Frauschi/Funktionsgenerator/Bilder/Gerät/Frontansicht.png

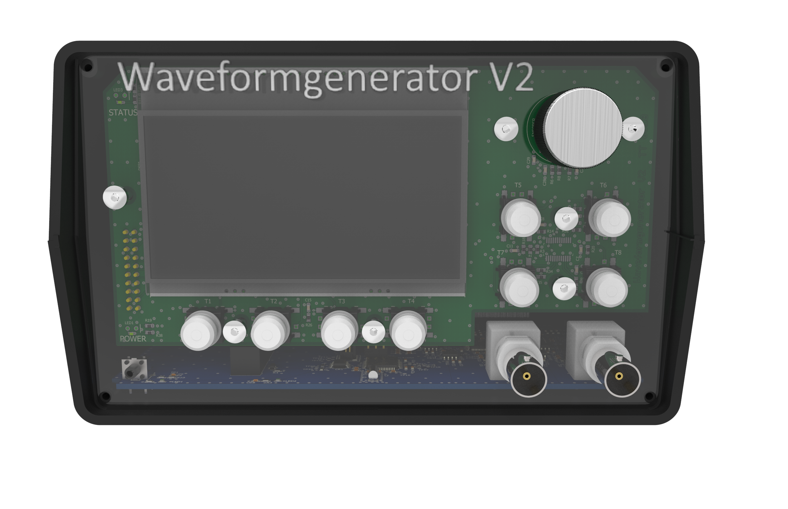
Bilder/Gerät/Frontansicht.png
