Frauschi/Funktionsgenerator/Bilder/Gerät/Frontpanel.png

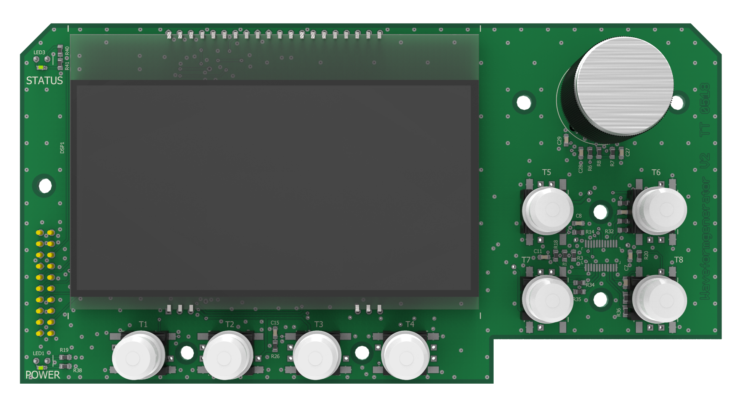
Bilder/Gerät/Frontpanel.png
