Frauschi/Funktionsgenerator/Bilder/Gerät/Funktionsgenerator_fertig2.jpg

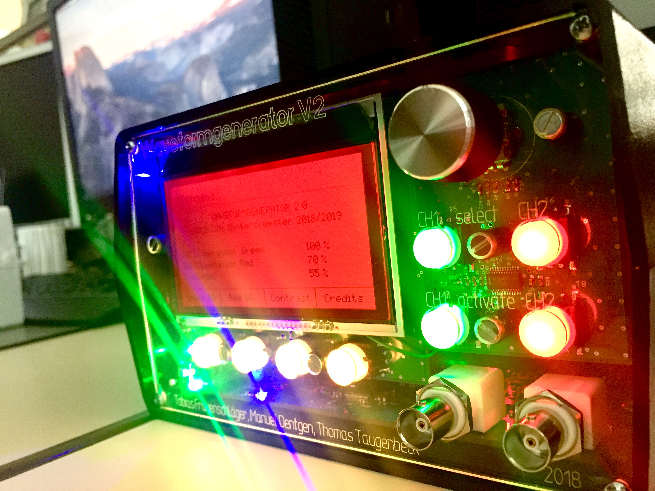
Bilder/Gerät/Funktionsgenerator_fertig2.jpg
