Frauschi/Funktionsgenerator/Bilder/Gerät/Innenansicht_oben.png

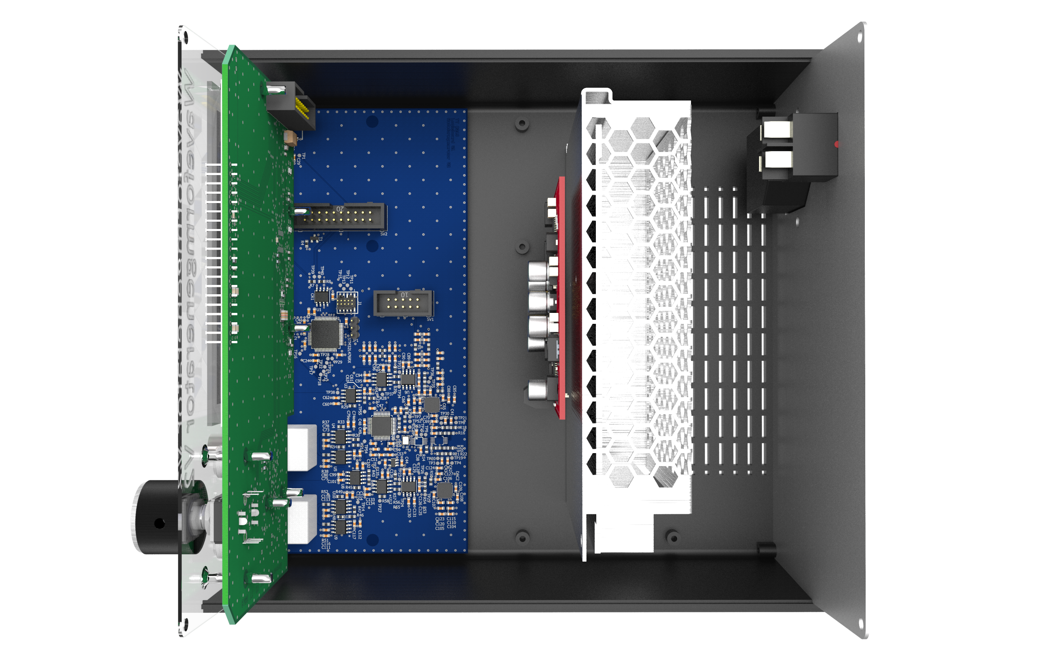
Bilder/Gerät/Innenansicht_oben.png
