Frauschi/Funktionsgenerator/Bilder/Gerät/Rückansicht.jpg

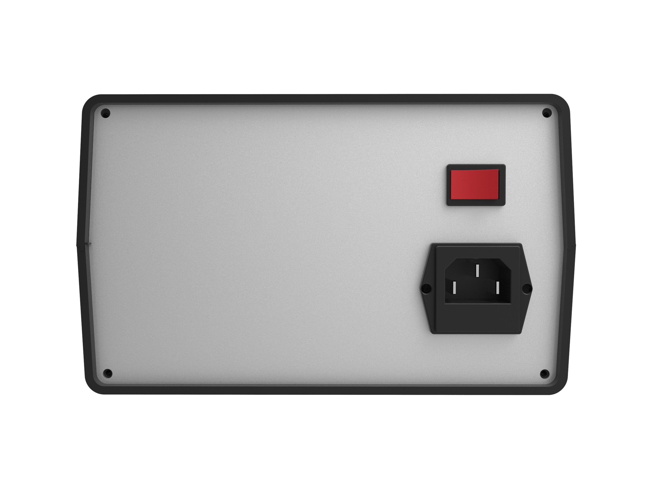
Bilder/Gerät/Rückansicht.jpg
