Frauschi/Funktionsgenerator/Bilder/Signale/Rect_1Hz.png

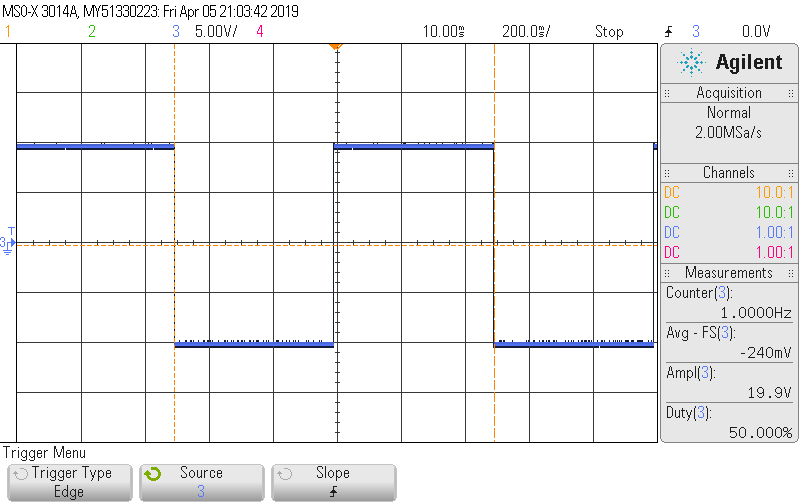
Bilder/Signale/Rect_1Hz.png
