Frauschi/Funktionsgenerator/Bilder/Signale/Rect_1MHz.png

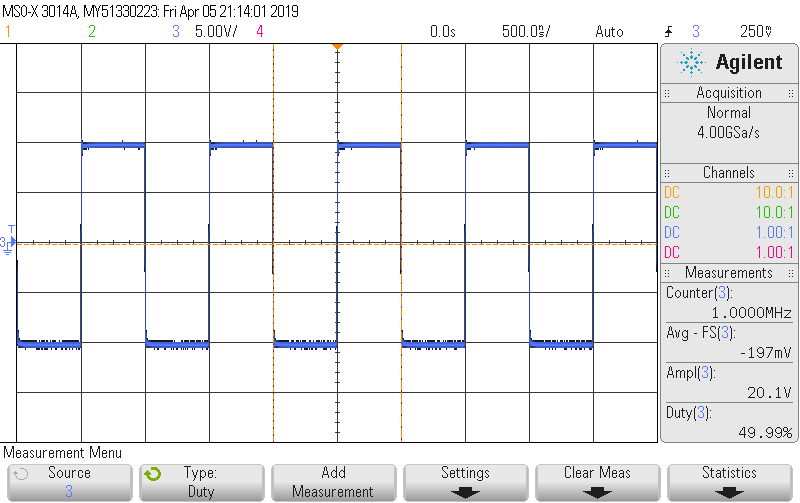
Bilder/Signale/Rect_1MHz.png
