Frauschi/Funktionsgenerator/Bilder/Signale/Rect_1MHz_10%.png

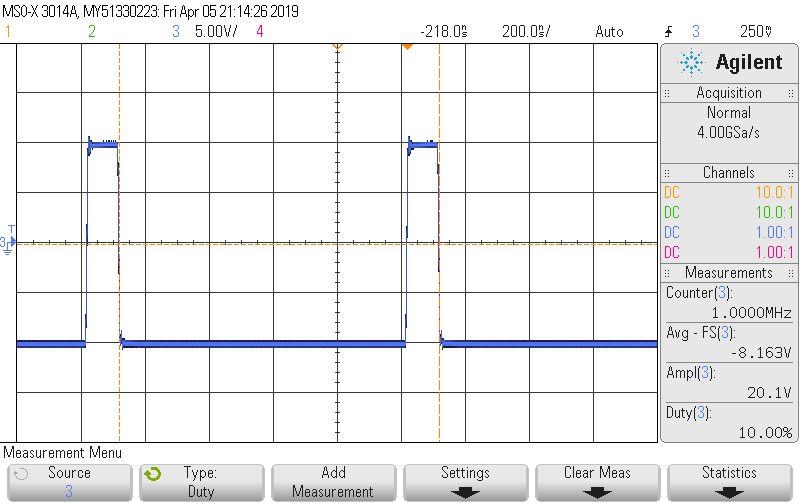
Bilder/Signale/Rect_1MHz_10%.png
