Frauschi/Funktionsgenerator/Bilder/Signale/Rect_1MHz_90%.png

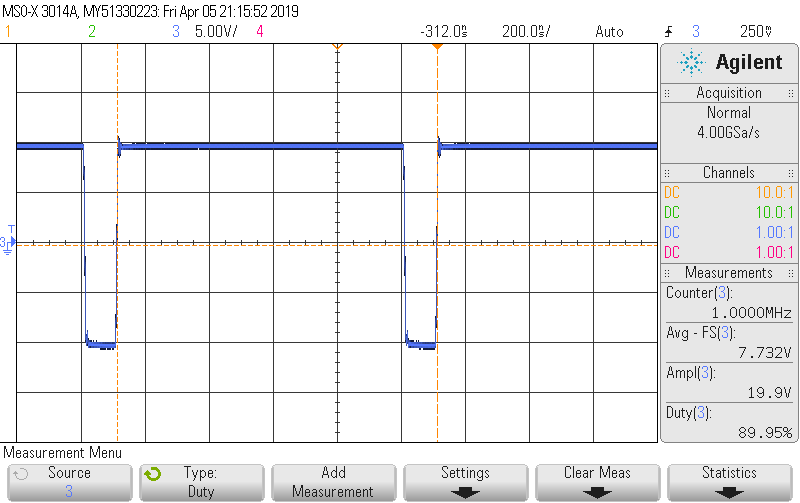
Bilder/Signale/Rect_1MHz_90%.png
