Frauschi/Funktionsgenerator/Bilder/Signale/Rect_10MHz.png

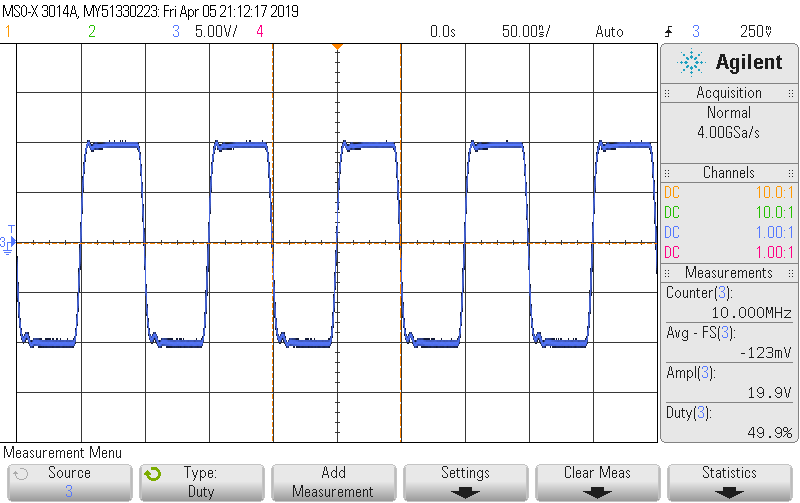
Bilder/Signale/Rect_10MHz.png
