Frauschi/Funktionsgenerator/Bilder/Signale/Saw_neg_1Hz.png

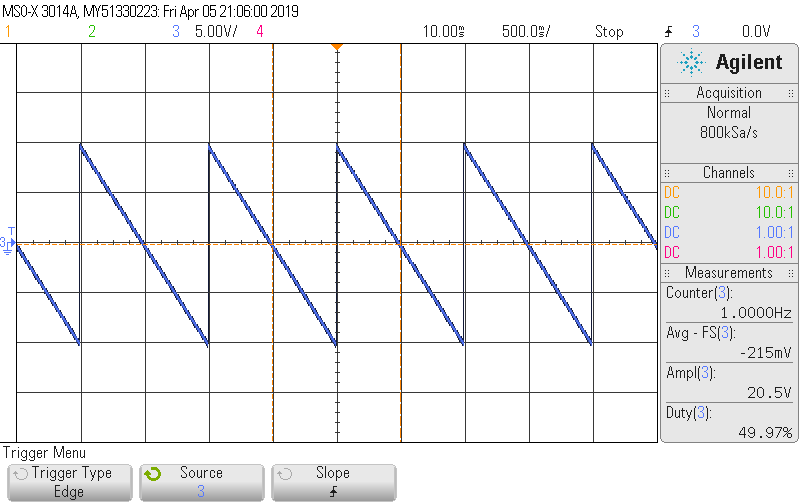
Bilder/Signale/Saw_neg_1Hz.png
