Frauschi/Funktionsgenerator/Bilder/Signale/Sine_1MHz_2Vpp_1V_Offset.png

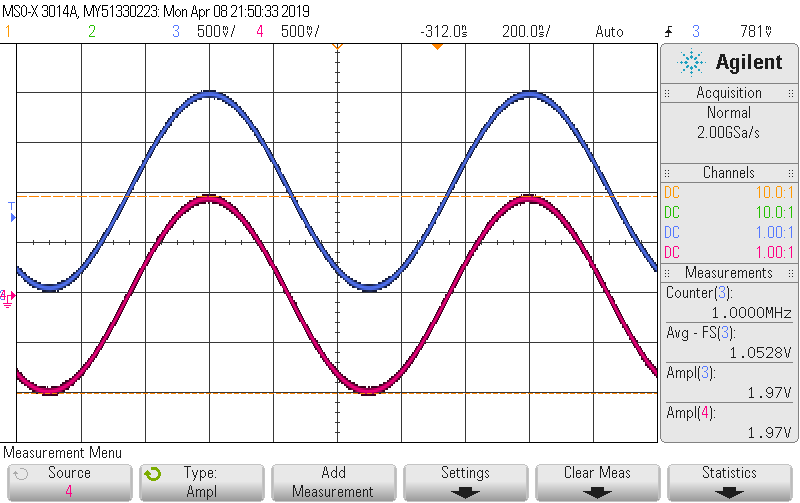
Bilder/Signale/Sine_1MHz_2Vpp_1V_Offset.png
