Frauschi/Funktionsgenerator/Bilder/Signale/Sine_1MHz_45deg.png

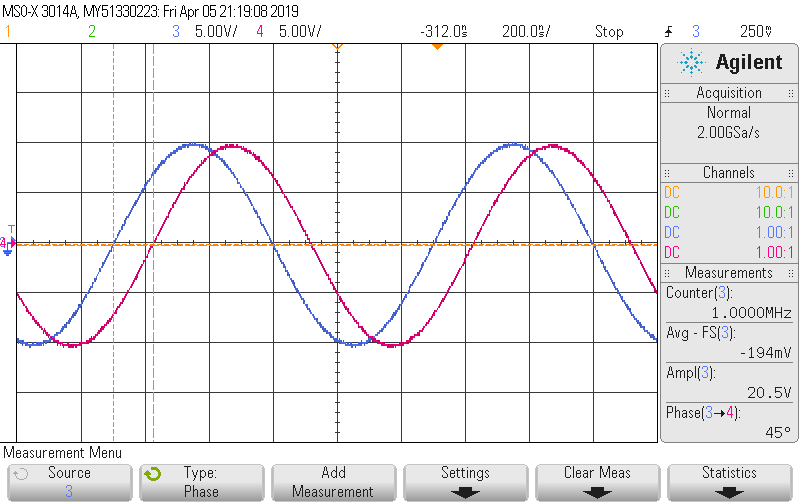
Bilder/Signale/Sine_1MHz_45deg.png
