Frauschi/Funktionsgenerator/Bilder/Signale/Sine_1MHz_180deg.png

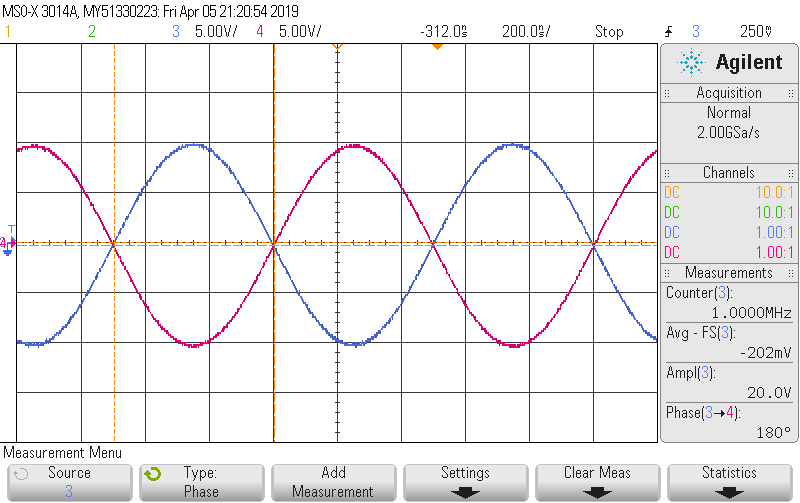
Bilder/Signale/Sine_1MHz_180deg.png
