Frauschi/Funktionsgenerator/Bilder/Signale/Sine_10MHz.png

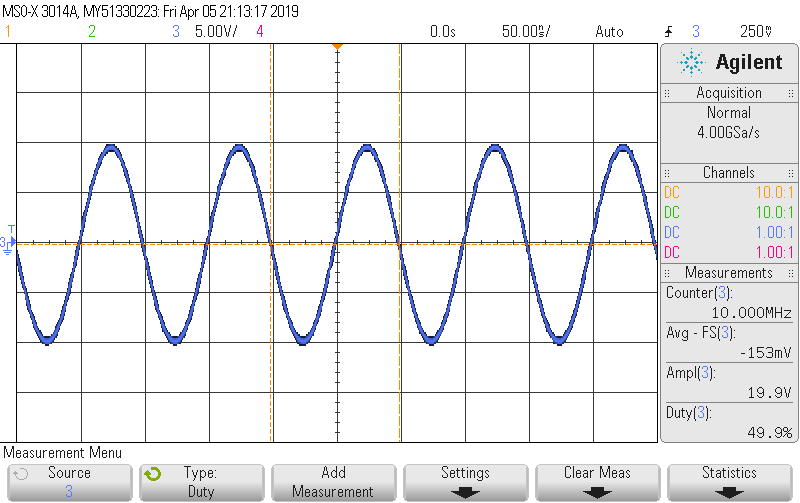
Bilder/Signale/Sine_10MHz.png
